andre94/clawd-airpods4-anc-case/assets/reference/airpods-4/textures/HRDjIYtbpAAYsXT.png

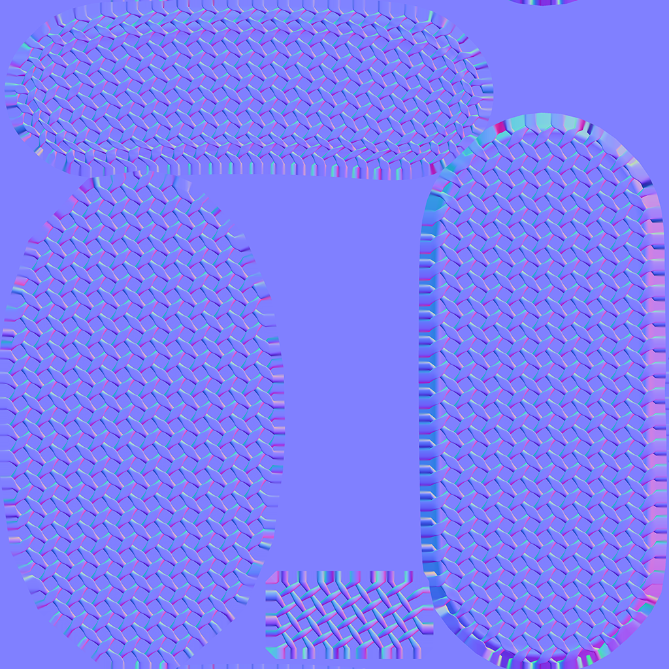
assets/reference/airpods-4/textures/HRDjIYtbpAAYsXT.png
