andre94/clawd-airpods4-anc-case/assets/reference/airpods-4/textures/jCnUEPXiviHNYTn.jpg

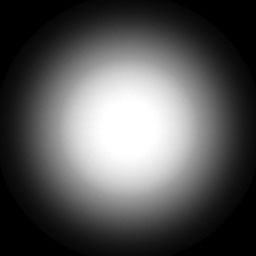
assets/reference/airpods-4/textures/jCnUEPXiviHNYTn.jpg
