andre94/clawd-airpods4-anc-case/docs/images/clawd-v03-hole-detail.png

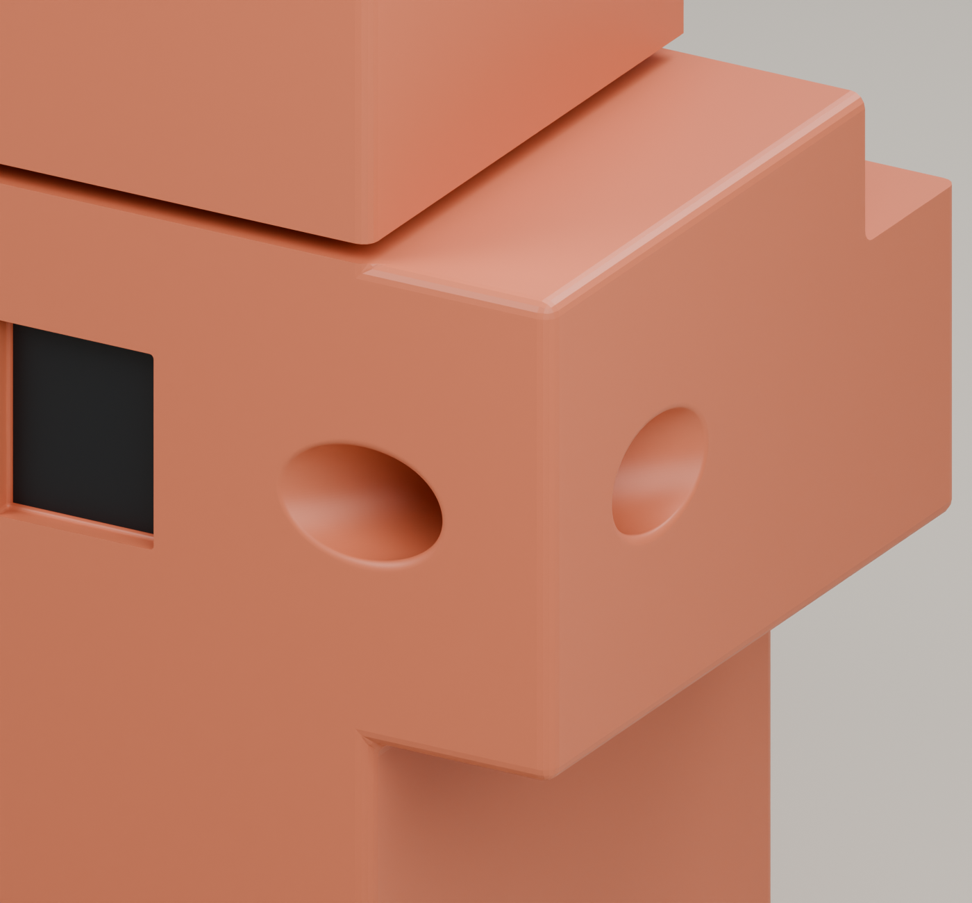
docs/images/clawd-v03-hole-detail.png
