andre94/clawd-airpods4-anc-case/docs/images/clawd-v03-rear.png

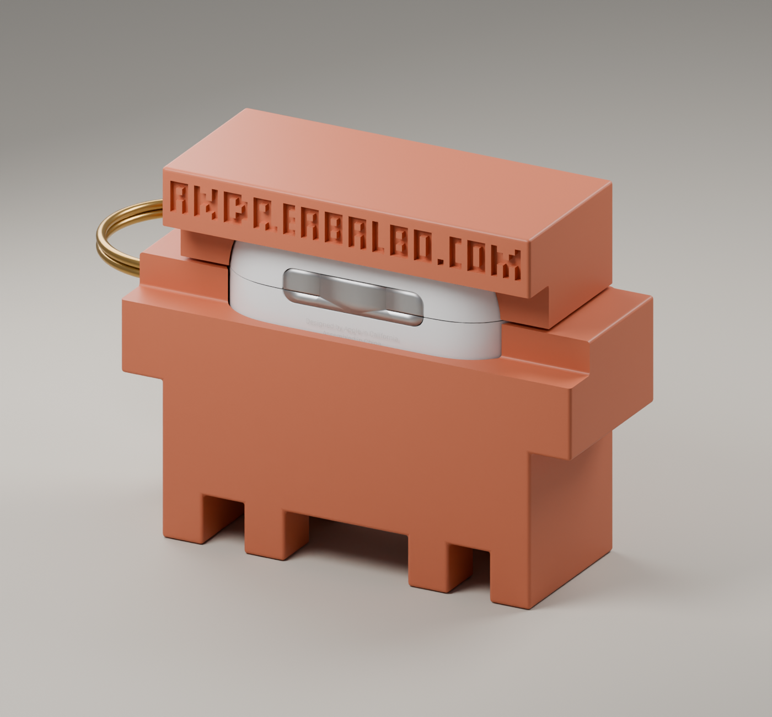
docs/images/clawd-v03-rear.png
