andre94/clawd-airpods4-anc-case/docs/images/clawd-v04-pad-seats.png

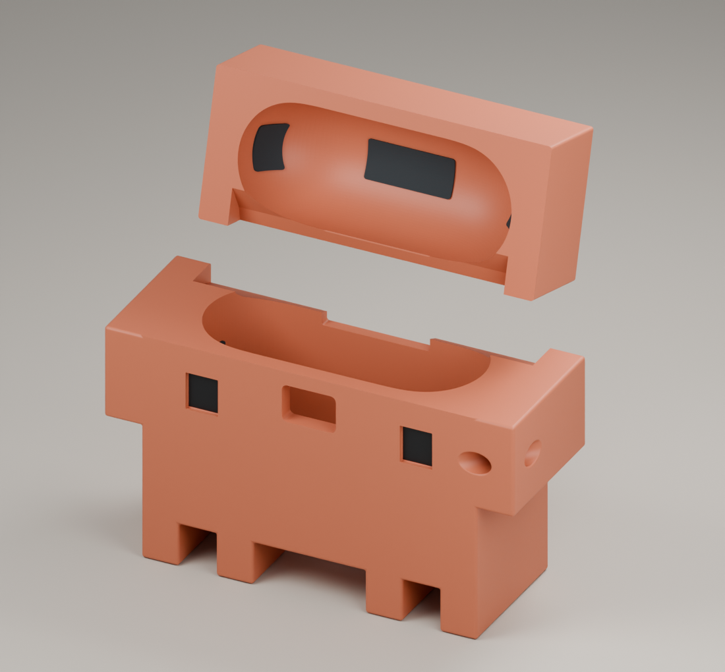
docs/images/clawd-v04-pad-seats.png
