andre94/clawd-airpods4-anc-case/docs/images/clawd-v04-underside.png

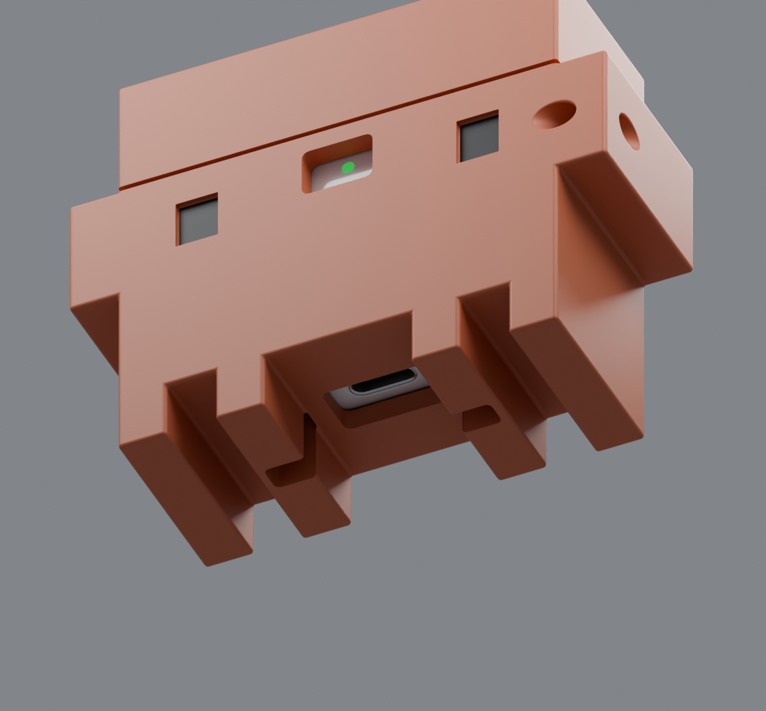
docs/images/clawd-v04-underside.png
